frank26080115/DummyLoad/LufaUsbAspLoader/Descriptors.c

/*
             LUFA Library
     Copyright (C) Dean Camera, 2012.

  dean [at] fourwalledcubicle [dot] com
           www.lufa-lib.org
*/

/*
  Copyright 2012  Dean Camera (dean [at] fourwalledcubicle [dot] com)

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
  The author disclaim all warranties with regard to this
  software, including all implied warranties of merchantability
  and fitness.  In no event shall the author be liable for any
  special, indirect or consequential damages or any damages
  whatsoever resulting from loss of use, data or profits, whether
  in an action of contract, negligence or other tortious action,
  arising out of or in connection with the use or performance of
  this software.
*/

/** \file
 *
 *  USB Device Descriptors, for library use when in USB device mode. Descriptors are special
 *  computer-readable structures which the host requests upon device enumeration, to determine
 *  the device's capabilities and functions.
 */

#include "Descriptors.h"

/** Device descriptor structure. This descriptor, located in FLASH memory, describes the overall
 *  device characteristics, including the supported USB version, control endpoint size and the
 *  number of device configurations. The descriptor is read out by the USB host when the enumeration
 *  process begins.
 */
const USB_Descriptor_Device_t PROGMEM DeviceDescriptor =
{
    .Header                 = {.Size = sizeof(USB_Descriptor_Device_t), .Type = DTYPE_Device},

    .USBSpecification       = VERSION_BCD(01.10),
    .Class                  = 0xFF,
    .SubClass               = 0,
    .Protocol               = 0,

    .Endpoint0Size          = FIXED_CONTROL_ENDPOINT_SIZE,

    // modified to behave like a USBasp
    .VendorID               = 0x16c0,
    .ProductID              = 0x05dc,
    .ReleaseNumber          = VERSION_BCD(1.2),

    .ManufacturerStrIndex   = 0x01,
    .ProductStrIndex        = 0x02,
    .SerialNumStrIndex      = NO_DESCRIPTOR,

    .NumberOfConfigurations = FIXED_NUM_CONFIGURATIONS
};

/** Configuration descriptor structure. This descriptor, located in FLASH memory, describes the usage
 *  of the device in one of its supported configurations, including information about any device interfaces
 *  and endpoints. The descriptor is read out by the USB host during the enumeration process when selecting
 *  a configuration so that the host may correctly communicate with the USB device.
 */
const USB_Descriptor_Configuration_t PROGMEM ConfigurationDescriptor =
{
    .Config =
        {
            .Header                 = {.Size = sizeof(USB_Descriptor_Configuration_Header_t), .Type = DTYPE_Configuration},

            .TotalConfigurationSize = sizeof(USB_Descriptor_Configuration_t),
            .TotalInterfaces        = 1,

            .ConfigurationNumber    = 1,
            .ConfigurationStrIndex  = NO_DESCRIPTOR,

            .ConfigAttributes       = USB_CONFIG_ATTR_RESERVED,

            .MaxPowerConsumption    = USB_CONFIG_POWER_MA(100)
        },

    .USBasp_Interface =
        {
            .Header                 = {.Size = sizeof(USB_Descriptor_Interface_t), .Type = DTYPE_Interface},

            .InterfaceNumber        = 0x00,
            .AlternateSetting       = 0x00,

            .TotalEndpoints         = 0,

            .Class                  = 0,
            .SubClass               = 0,
            .Protocol               = 0,

            .InterfaceStrIndex      = NO_DESCRIPTOR
        },
};

/** Language descriptor structure. This descriptor, located in FLASH memory, is returned when the host requests
 *  the string descriptor with index 0 (the first index). It is actually an array of 16-bit integers, which indicate
 *  via the language ID table available at USB.org what languages the device supports for its string descriptors.
 */
const USB_Descriptor_String_t PROGMEM USBasp_LanguageString =
{
    .Header                 = {.Size = USB_STRING_LEN(1), .Type = DTYPE_String},

    .UnicodeString          = {LANGUAGE_ID_ENG}
};

/** Manufacturer descriptor string. This is a Unicode string containing the manufacturer's details in human readable
 *  form, and is read out upon request by the host when the appropriate string ID is requested, listed in the Device
 *  Descriptor.
 */
const USB_Descriptor_String_t PROGMEM USBasp_ManufacturerString =
{
    .Header                 = {.Size = USB_STRING_LEN(13), .Type = DTYPE_String},

    .UnicodeString          = L"www.fischl.de"
};

/** Product descriptor string. This is a Unicode string containing the product's details in human readable form,
 *  and is read out upon request by the host when the appropriate string ID is requested, listed in the Device
 *  Descriptor.
 */
const USB_Descriptor_String_t PROGMEM USBasp_ProductString =
{
    .Header                 = {.Size = USB_STRING_LEN(6), .Type = DTYPE_String},

    .UnicodeString          = L"USBasp"
};

/** This function is called by the library when in device mode, and must be overridden (see library "USB Descriptors"
 *  documentation) by the application code so that the address and size of a requested descriptor can be given
 *  to the USB library. When the device receives a Get Descriptor request on the control endpoint, this function
 *  is called so that the descriptor details can be passed back and the appropriate descriptor sent back to the
 *  USB host.
 */
uint16_t CALLBACK_USB_GetDescriptor(const uint16_t wValue,
                                    const uint8_t wIndex,
                                    const void** const DescriptorAddress)
{
    const uint8_t DescriptorType   = (wValue >> 8);
    const uint8_t  DescriptorNumber = (wValue & 0xFF);

    const void* Address = NULL;
    uint16_t    Size    = NO_DESCRIPTOR;

    /* If/Else If chain compiles slightly smaller than a switch case */
    if (DescriptorType == DTYPE_Device)
    {
        Address = &DeviceDescriptor;
        Size    = sizeof(USB_Descriptor_Device_t);
    }
    else if (DescriptorType == DTYPE_Configuration)
    {
        Address = &ConfigurationDescriptor;
        Size    = sizeof(USB_Descriptor_Configuration_t);
    }
    else if (DescriptorType == DTYPE_String)
    {
        if (DescriptorNumber == 0x00)
        {
            Address = &USBasp_LanguageString;
            Size    = pgm_read_byte(&USBasp_LanguageString.Header.Size);
        }
        else if (DescriptorNumber == 0x01)
        {
            Address = &USBasp_ManufacturerString;
            Size    = pgm_read_byte(&USBasp_ManufacturerString.Header.Size);
        }
        else if (DescriptorNumber == 0x02)
        {
            Address = &USBasp_ProductString;
            Size    = pgm_read_byte(&USBasp_ProductString.Header.Size);
        }
    }

    *DescriptorAddress = Address;
    return Size;
}
